AdiUliel/Pip-LLM-Tutor/Documentation/Hardware Documentation/canvas16.png

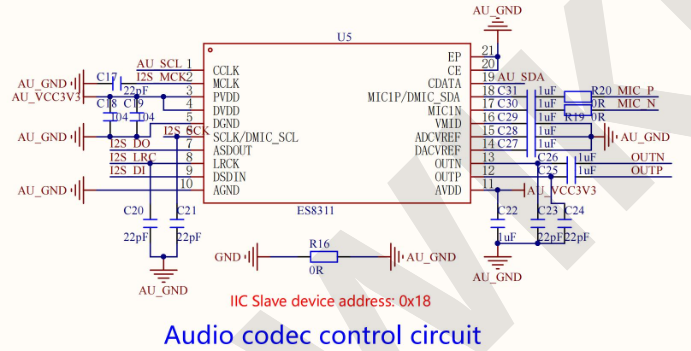
Documentation/Hardware Documentation/canvas16.png
