AdiUliel/Pip-LLM-Tutor/Documentation/turn-sequence-diagram.png

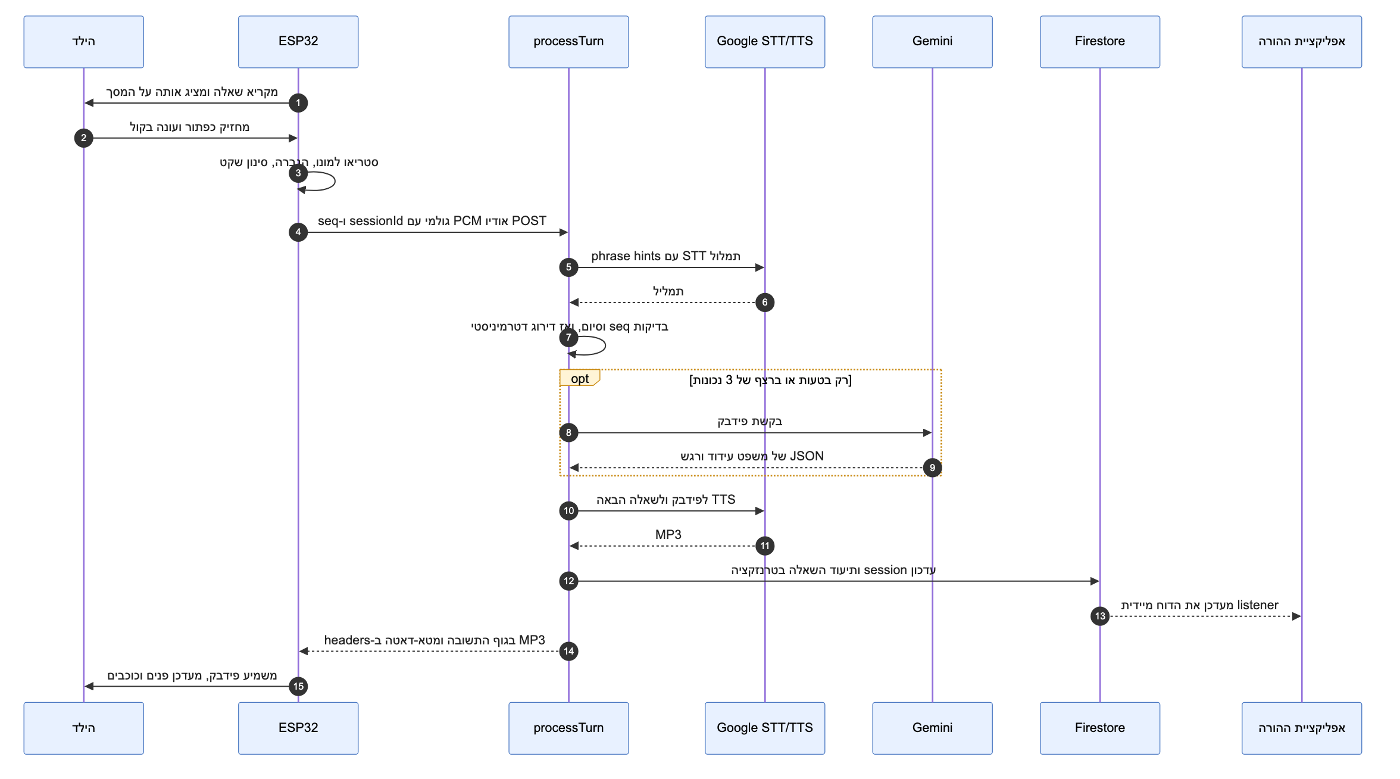
Documentation/turn-sequence-diagram.png
