AdiUliel/Pip-LLM-Tutor/ESP32/homework_assistant/es8311.h

#pragma once
#include <Wire.h>
#include "pins.h"

// Master DAC (speaker) digital volume — ES8311 reg 0x32: 0.5 dB/step,
// 0xBF = 0 dB (unity), higher hex = louder. 0xC5 ≈ +3 dB, a bit louder since the
// speaker opening is partly covered. Exposed so firmware can change loudness at
// runtime (e.g. the low-volume bench-testing toggle). Back off toward 0xBF if
// loud TTS distorts — it's pure digital gain, so it can clip near-full-scale
// source peaks (watch the "peak=…/32767" line in tts_player).
#define ES8311_DAC_VOL_DEFAULT 0xC5

// ─────────────────────────────────────────────────────────────────────────────
// ES8311 Audio Codec Driver — derived from official LCD Wiki example
// (Example_17_echo / Example_16_music / es8311.cpp)
//
// MCLK = 384 × 16000 = 6.144 MHz  (I2S_MCLK_MULTIPLE_384 in i2s_start_recording)
// BCLK = 6144000 / (bclk_div=4) = ... actually set by I2S driver automatically
// LRCK = 16000 Hz
// Slot width: 16-bit stereo (32 BCLK per LRCK)
// ─────────────────────────────────────────────────────────────────────────────

static void es8311_write(uint8_t reg, uint8_t val) {
  Wire.beginTransmission(ES8311_I2C_ADDR);
  Wire.write(reg);
  Wire.write(val);
  Wire.endTransmission();
}

bool initES8311() {
  Wire.begin(PIN_I2C_SDA, PIN_I2C_SCL);

  // Verify codec is on the I2C bus
  Wire.beginTransmission(ES8311_I2C_ADDR);
  if (Wire.endTransmission() != 0) {
    Serial.println("[ES8311] Not found on I2C bus! Check wiring.");
    return false;
  }

  // ── Reset ─────────────────────────────────────────────────────────────────
  es8311_write(0x00, 0x1F);   // Soft reset all registers
  delay(20);
  es8311_write(0x00, 0x00);   // Clear reset
  es8311_write(0x00, 0x80);   // Power-on command — required after reset

  // ── Clock: MCLK pin → 6.144 MHz (384 × 16 kHz) ───────────────────────────
  // Coefficients from official coeff_div table for {6144000, 16000}:
  //   pre_div=3, pre_multi=1, bclk_div=4, lrck=0x00/0xFF, osr=0x10
  es8311_write(0x01, 0x3F);   // Enable all clocks, MCLK from MCLK pin
  es8311_write(0x02, 0x48);   // pre_div=3→(2<<5)=0x40, pre_multi=1→(1<<3)=0x08
  es8311_write(0x03, 0x10);   // fs_mode=0, adc_osr=0x10
  es8311_write(0x04, 0x10);   // dac_osr=0x10
  es8311_write(0x05, 0x00);   // adc_div=1, dac_div=1
  es8311_write(0x06, 0x03);   // bclk_div=4 → 4-1=3
  es8311_write(0x07, 0x00);   // lrck_h
  es8311_write(0x08, 0xFF);   // lrck_l

  // ── I2S format: 16-bit (ES8311_RESOLUTION_16 → 3<<2 = 0x0C) ─────────────
  es8311_write(0x09, 0x0C);   // SDP In  (ADC→I2S) 16-bit I2S
  es8311_write(0x0A, 0x0C);   // SDP Out (I2S→DAC) 16-bit I2S

  // ── Power up ──────────────────────────────────────────────────────────────
  es8311_write(0x0D, 0x01);   // Power up analog circuitry
  es8311_write(0x0E, 0x02);   // Enable analog PGA + ADC modulator
  es8311_write(0x12, 0x00);   // Power up DAC
  es8311_write(0x13, 0x10);   // Enable output to HP drive

  // ── Microphone (analog, not PDM) ──────────────────────────────────────────
  es8311_write(0x14, 0x1A);   // Enable analog MIC, DIFFERENTIAL, +PGA (official board value)
                                // This board (per the LCD Wiki ai_chat demo) wires the mic
                                // differentially; single-ended (0x10) picks up only constant
                                // clock/common-mode crosstalk instead of the voice.
  // ADC digital volume, 0.5 dB per step. 0xE0 ≈ +12 dB so quiet / far-field
  // speech reaches STT at a usable level, while normal speech stays ~-19 dBFS
  // with headroom. If a loud close answer clips (watch "peak=…/32767" and the
  // [Audio]/[Main] RMS serial logs), lower toward 0xDA.
  es8311_write(0x17, 0xE0);   // ADC digital volume (~+12dB for a louder capture)

  // ── ADC high-pass filter — removes DC offset (two-stage) ──────────────────
  // Both stages must be written (as in the Espressif/arduino-audio-driver
  // init); without the HPF a DC offset rails the ADC and drowns the speech.
  es8311_write(0x1B, 0x0A);   // ADC HPF stage 1 + ALC automute
  es8311_write(0x1C, 0x6A);   // ADC HPF stage 2 + EQ bypass

  // ── DAC equalizer bypass ──────────────────────────────────────────────────
  es8311_write(0x37, 0x08);   // Bypass DAC EQ

  // ── DAC volume (TTS loudness) — see ES8311_DAC_VOL_DEFAULT at top of file ──
  es8311_write(0x32, ES8311_DAC_VOL_DEFAULT);

  Serial.println("[ES8311] Init OK");
  return true;
}

// ── Runtime DAC (speaker) volume ──────────────────────────────────────────────
// reg 0x32: 0.5 dB/step, 0xBF = 0 dB (unity), higher hex = louder. Lets firmware
// change TTS loudness after init — used by the low-volume bench-testing toggle.
static void es8311SetDacVolume(uint8_t vol) {
  es8311_write(0x32, vol);
}
